K4LCIFER/thermometer-digital-min_max/firmware/inc/pins.h

#ifndef __PINS_H__
#define __PINS_H__

#include "atmega328p_utils.h"

extern const pin_t sensor_data_pin;
extern const pin_t ss_segment_pins[8];
extern const pin_t ss_enable_pins[4];
extern const pin_t reset_saved_temps_btn_pin;
extern const pin_t disp_min_temp_btn_pin;
extern const pin_t disp_max_temp_btn_pin;
extern const pin_t disp_current_temp_btn_pin;

#endif
